mistic100/IV-27-Clock/schematics/IV-27 clock.kicad_sch

## KiCad design schematics/IV-27 clock.kicad_sch (2025-04-08)

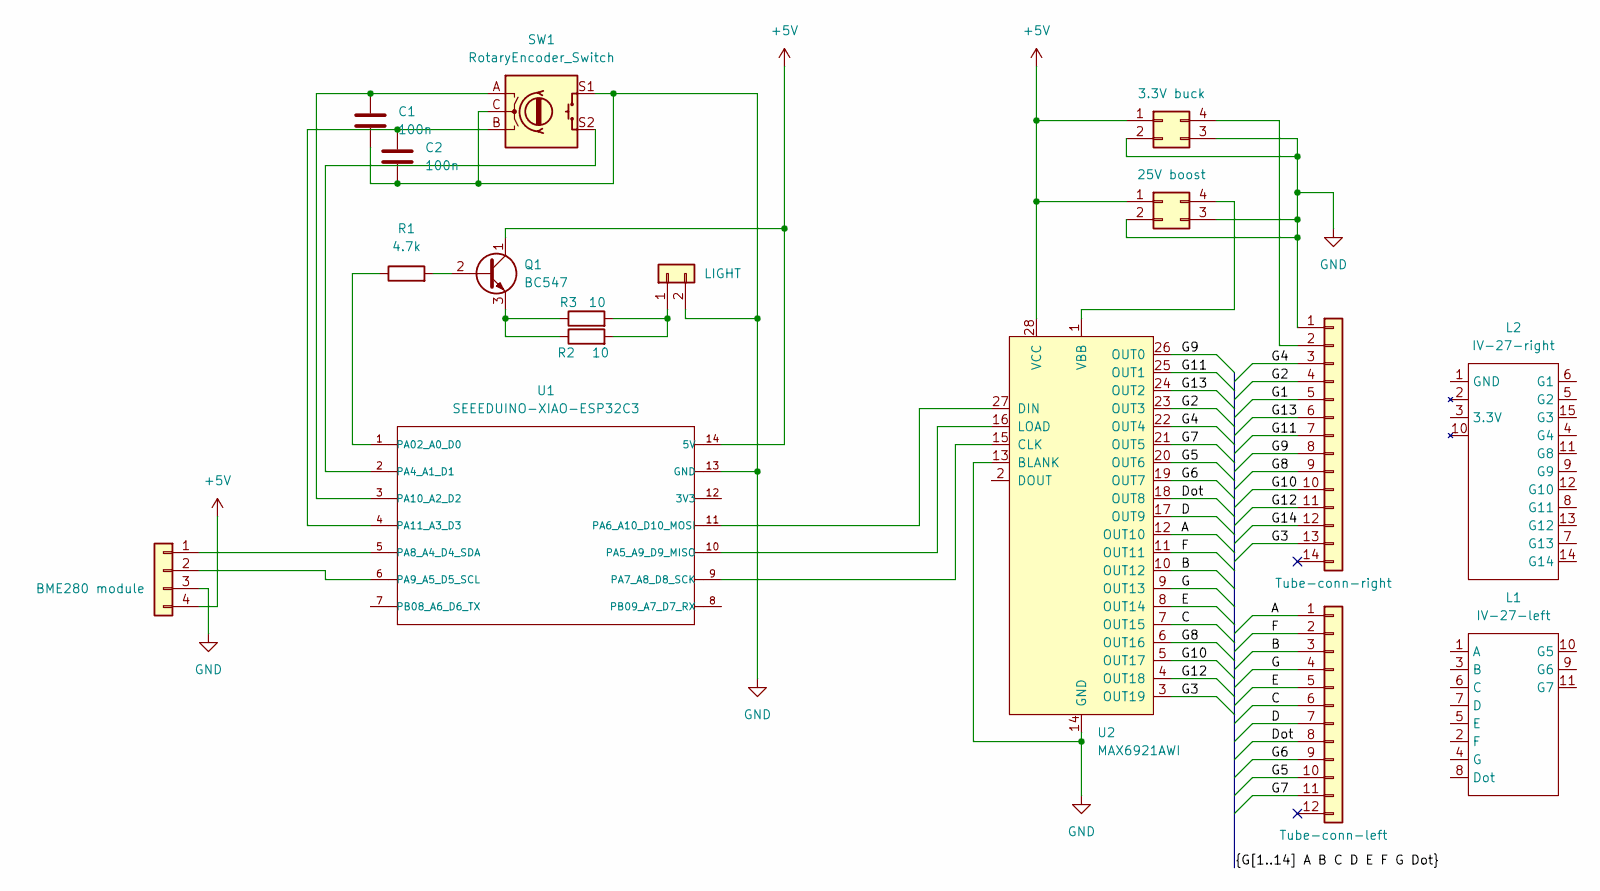
[picture p2: schematic IV-27 clock.kicad_sch]

Parts:
C1, C2: 100n
J1: BME280 module
J2: LIGHT
J3: 3.3V buck
J4: 25V boost
L1: IV-27-left
L2: IV-27-right
Q1: BC547; TO-92_Inline
R1: 4.7k
R2, R3: 10
SW1: RotaryEncoder_Switch
Tube-conn-left: Conn_02x06_Counter_Clockwise; PinHeader_2x06_P2.54mm_Vertical
Tube-conn-right: Conn_02x07_Counter_Clockwise; PinHeader_2x07_P2.54mm_Vertical
U1: SEEEDUINO-XIAO-ESP32C3; MOUDLE14P-SMD-2.54-21X17.8MM
U2: MAX6921AWI

Connections:
+5V: J1.4, J3.1, J4.1, Q1.1 (C), U1.14 (5V), U2.28 (VCC)
A: Tube-conn-left.1, U2.12 (OUT10)
B: Tube-conn-left.3, U2.10 (OUT12)
C: Tube-conn-left.6, U2.7 (OUT15)
D: Tube-conn-left.7, U2.17 (OUT9)
Dot: Tube-conn-left.8, U2.18 (OUT8)
E: Tube-conn-left.5, U2.8 (OUT14)
F: Tube-conn-left.2, U2.11 (OUT11)
G: Tube-conn-left.4, U2.9 (OUT13)
G1: Tube-conn-right.5
G2: Tube-conn-right.4, U2.23 (OUT3)
G3: Tube-conn-right.13, U2.3 (OUT19)
G4: Tube-conn-right.3, U2.22 (OUT4)
G5: Tube-conn-left.10, U2.20 (OUT6)
G6: Tube-conn-left.9, U2.19 (OUT7)
G7: Tube-conn-left.11, U2.21 (OUT5)
G8: Tube-conn-right.9, U2.6 (OUT16)
G9: Tube-conn-right.8, U2.26 (OUT0)
G10: Tube-conn-right.10, U2.5 (OUT17)
G11: Tube-conn-right.7, U2.25 (OUT1)
G12: Tube-conn-right.11, U2.4 (OUT18)
G13: Tube-conn-right.6, U2.24 (OUT2)
G14: Tube-conn-right.12
GND: C1.2, C2.2, J1.3, J2.2, J3.2, J3.3, J4.2, J4.3, SW1.C, SW1.S1, Tube-conn-right.1, U1.13 (GND), U2.13 (BLANK), U2.14 (GND)
unnamed: C1.1, SW1.A, U1.3 (PA10_A2_D2)
unnamed: C2.1, SW1.B, U1.4 (PA11_A3_D3)
unnamed: J1.1, U1.5 (PA8_A4_D4_SDA)
unnamed: J1.2, U1.6 (PA9_A5_D5_SCL)
unnamed: J2.1, R2.2, R3.2
unnamed: J3.4, Tube-conn-right.2
unnamed: J4.4, U2.1 (VBB)
unnamed: Q1.2 (B), R1.2
unnamed: Q1.3 (E), R2.1, R3.1
unnamed: R1.1, U1.1 (PA02_A0_D0)
unnamed: SW1.S2, U1.2 (PA4_A1_D1)
unnamed: U1.9 (PA7_A8_D8_SCK), U2.15 (CLK)
unnamed: U1.10 (PA5_A9_D9_MISO), U2.16 (LOAD)
unnamed: U1.11 (PA6_A10_D10_MOSI), U2.27 (DIN)
